RoboticsClubIITK/StepXplorer-Summer-Project-2025-/Hardware/WhatsApp Image 2025-06-13 at 14.07.26_1ff2cb23.jpg

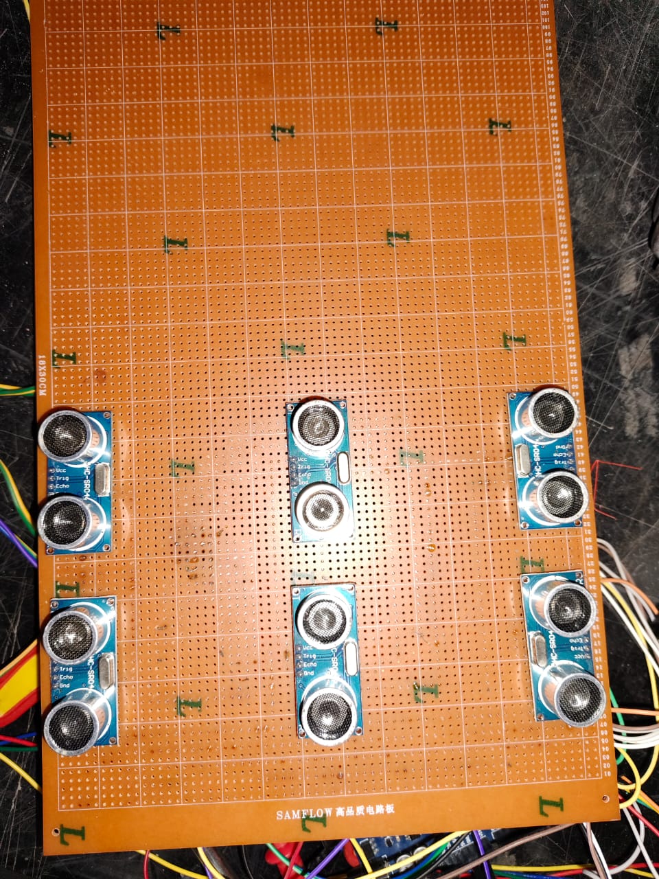
Hardware/WhatsApp Image 2025-06-13 at 14.07.26_1ff2cb23.jpg
